Gornist/_larphouse/step/5/блоки/щит_окно.step

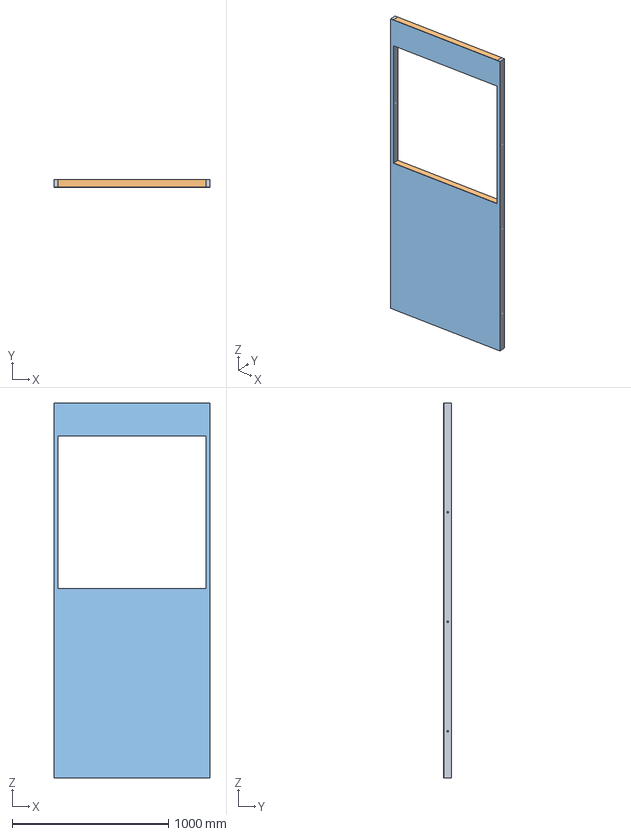
[picture p16: CAD file, 2026-10-09]
step/5/блоки/щит_окно.step
997.0 x 53.0 x 2400.0 mm
стойка_щита_25х50х2400 x 2
перемычка_25х50х947 x 4
обшивка_фанера_3мм_ 997х2400
