Gornist/_larphouse/step/5/блоки/прогон.step

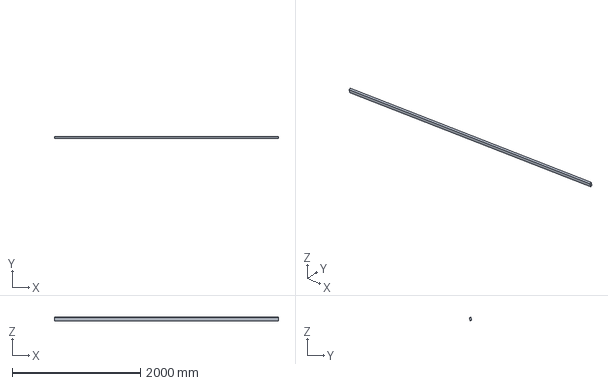
[picture p17: CAD file, 2026-10-09]
step/5/блоки/прогон.step
3500.0 x 38.9 x 55.2 mm
