Gornist/_larphouse/step/6/блоки/полуферма_Б_средняя.step

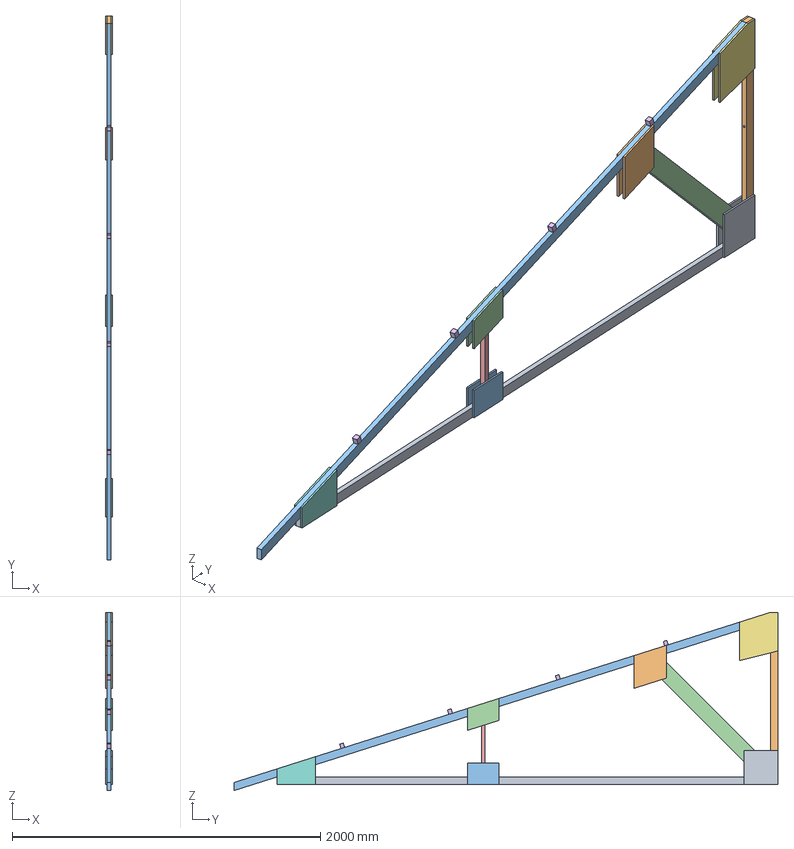
[picture p18: CAD file, 2026-10-09]
step/6/блоки/полуферма_Б_средняя.step
43.0 x 3530.0 x 1156.4 mm
затяжка_25х50х3250
стойка_фермы_25х50х1068
стропило_25х50х3651
подкос_25х50х1066
бабка_25х50х420
лапка_прогона_25х25х30 x 4
косынка_фанера_9 x 12
