Gornist/_larphouse/step/5/блоки/лежень.step

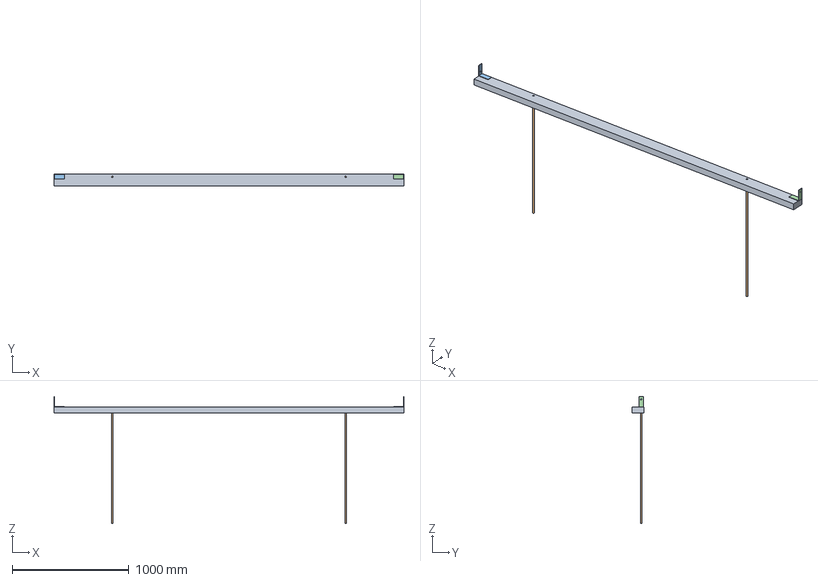
[picture p19: CAD file, 2026-10-09]
step/5/блоки/лежень.step
3000.0 x 100.0 x 1090.0 mm
лежень_50х100х2996
арматура_12х1000 x 2
уголок_90х90х40 x 2
