Gornist/_larphouse/step/5/блоки/щит_дверь.step

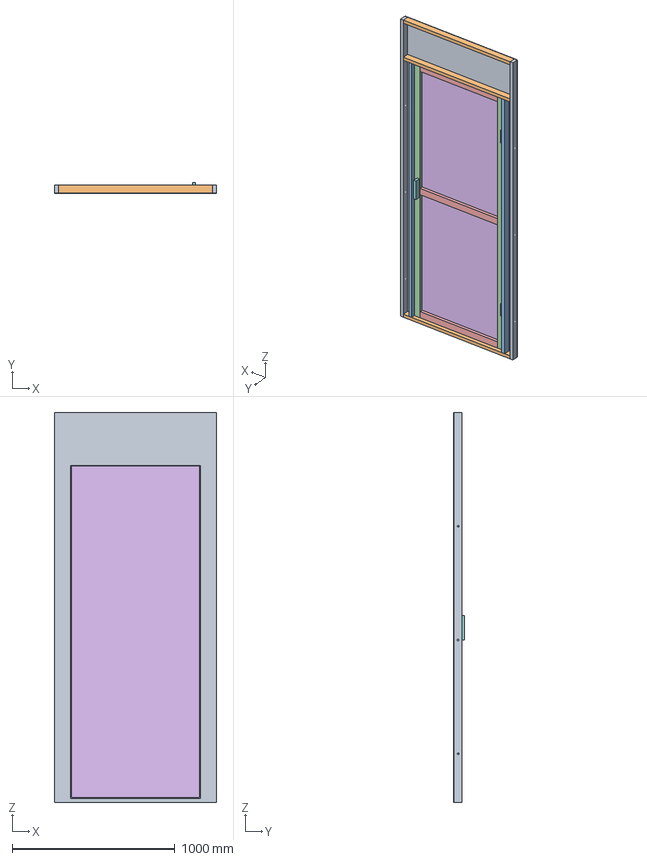
[picture p21: CAD file, 2026-10-09]
step/5/блоки/щит_дверь.step
997.0 x 68.0 x 2400.0 mm
стойка_щита_25х50х2400 x 2
перемычка_25х50х947 x 3
стойка_двери_25х50х2050 x 2
полотно_стойка_25х50х2040 x 2
полотно_перемычка_ 25х50х690.0 x 3
полотно_фанера_790х2040
петля_100 x 2
ручка
обшивка_фанера_3мм_ 997х2400
