Gornist/_larphouse/step/5/блоки/ригель_фронтонный.step

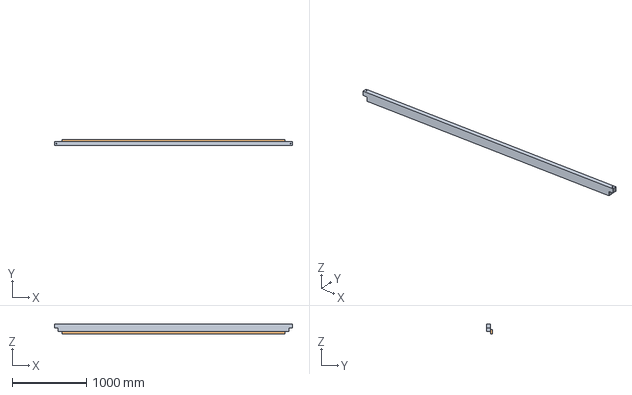
[picture p22: CAD file, 2026-10-09]
step/5/блоки/ригель_фронтонный.step
3200.0 x 79.0 x 130.0 mm
ригель_фронтонный_ 50х100х3200
рейка_упорная_Г_3000
