Gornist/_larphouse/step/5/блоки/ригель_карнизный.step

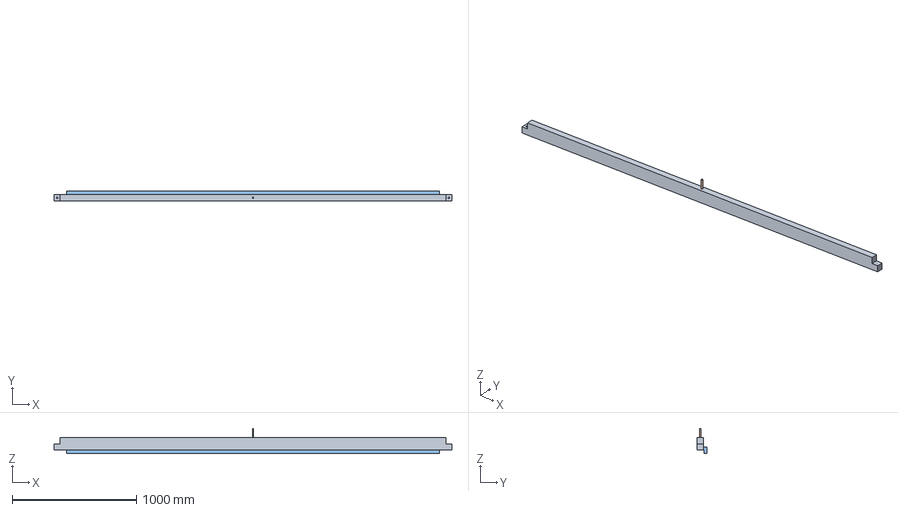
[picture p23: CAD file, 2026-10-09]
step/5/блоки/ригель_карнизный.step
3200.0 x 79.0 x 205.0 mm
ригель_карнизный_ 50х100х3200
штырь_12х165
рейка_упорная_Г_3000
