Gornist/_larphouse/step/5/img/дом_без_тента.png

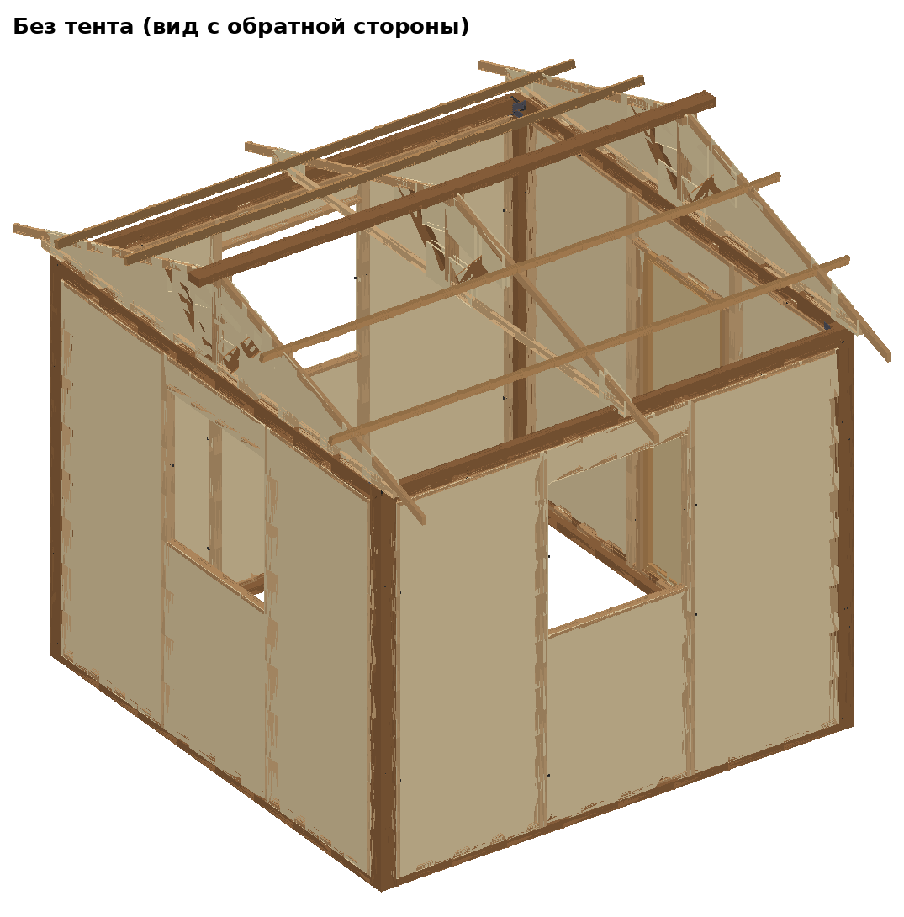
step/5/img/дом_без_тента.png
