Gornist/_larphouse/step/5/img/каркас.png

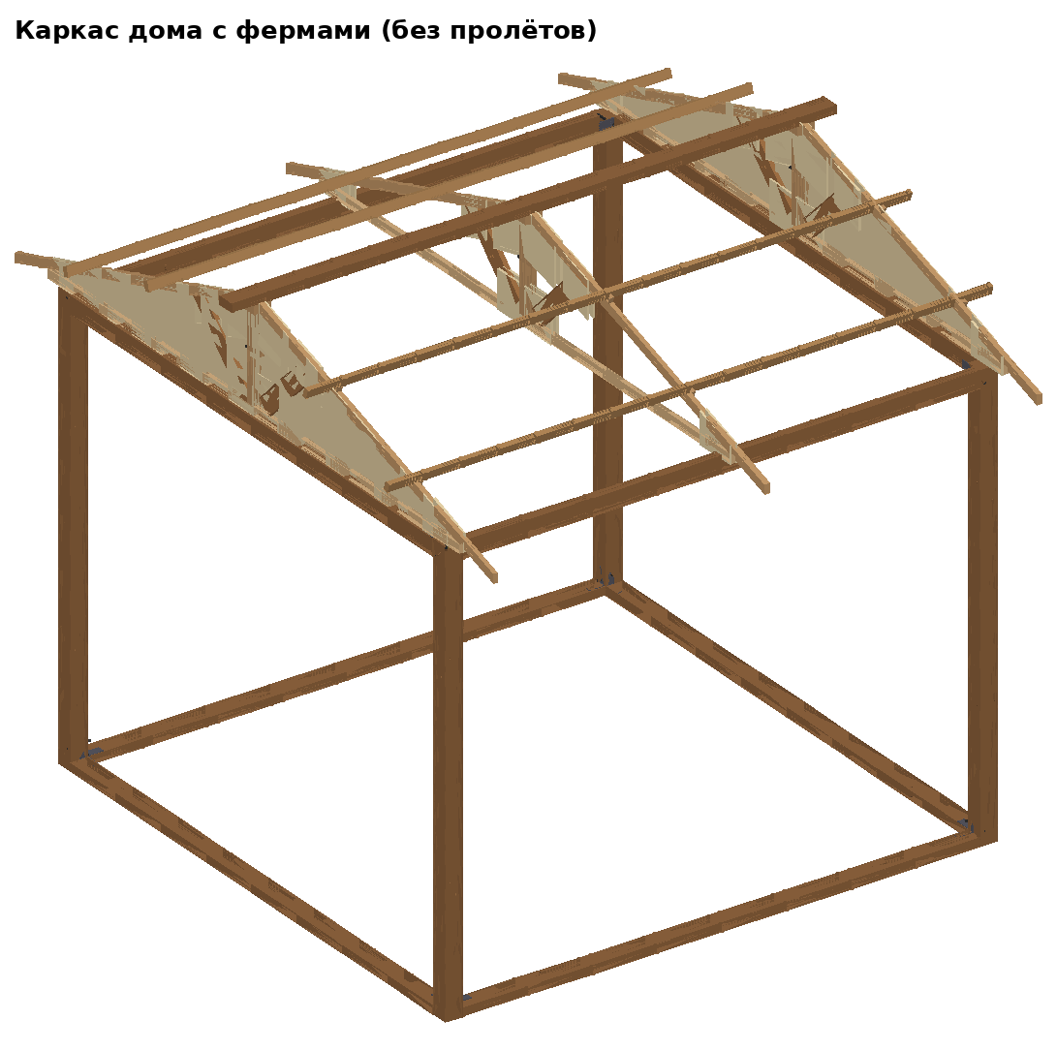
step/5/img/каркас.png
