Gornist/_larphouse/step/5/img/полуферма_фронтон_0.png

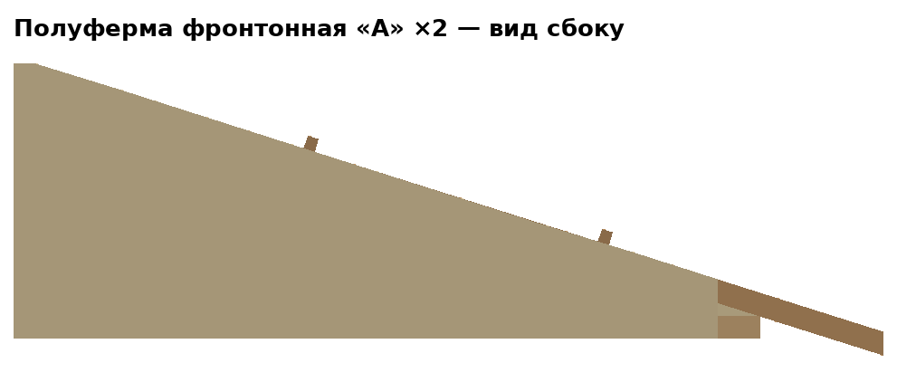
step/5/img/полуферма_фронтон_0.png
