Gornist/_larphouse/step/5/img/полуферма_фронтон_25.png

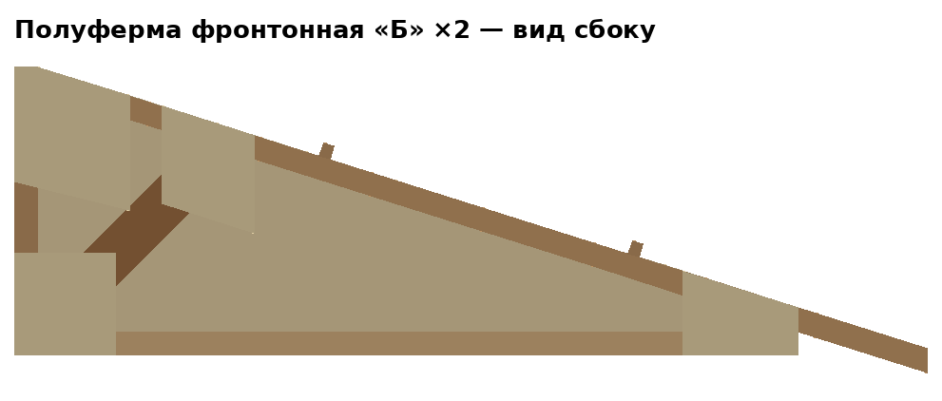
step/5/img/полуферма_фронтон_25.png
