Gornist/_larphouse/step/5/img/пролёт_дверь_снаружи.png

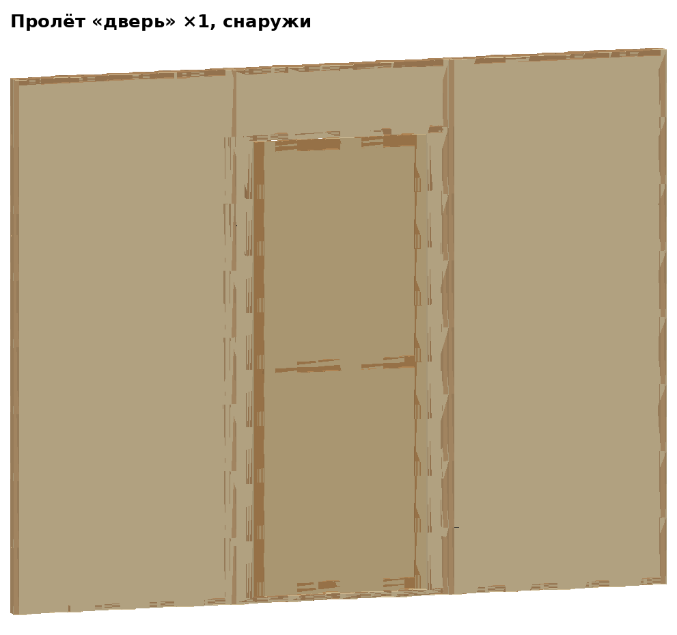
step/5/img/пролёт_дверь_снаружи.png
