Gornist/_larphouse/step/5/img/пролёт_окно_изнутри.png

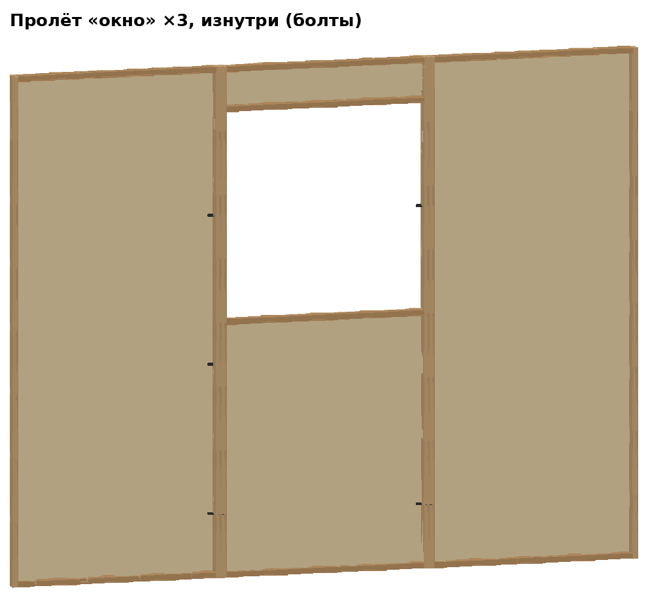
step/5/img/пролёт_окно_изнутри.png
