Gornist/_larphouse/step/6/3х6/img/без_тента.png

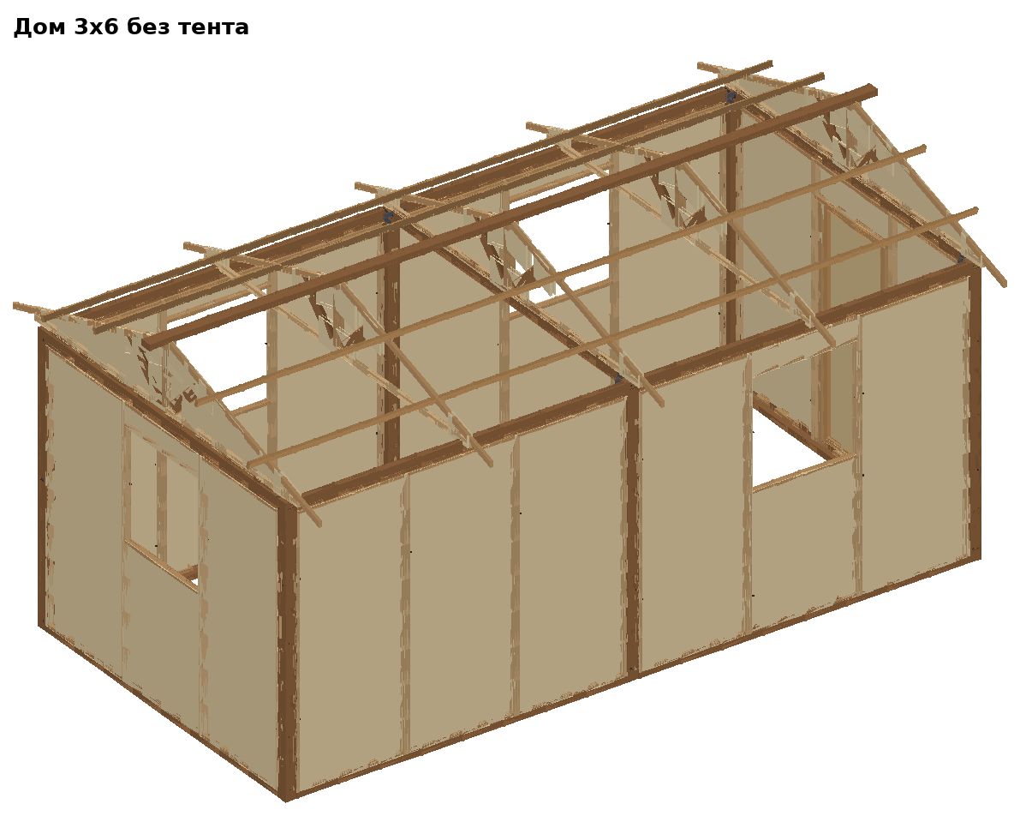
step/6/3х6/img/без_тента.png
