Gornist/_larphouse/step/6/3х6/img/план.png

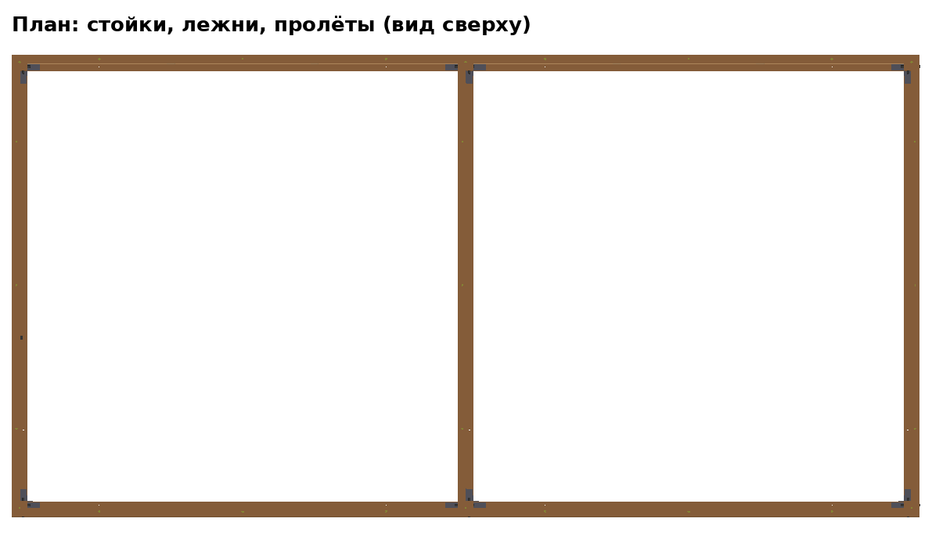
step/6/3х6/img/план.png
