Gornist/_larphouse/step/6/3х9/img/каркас.png

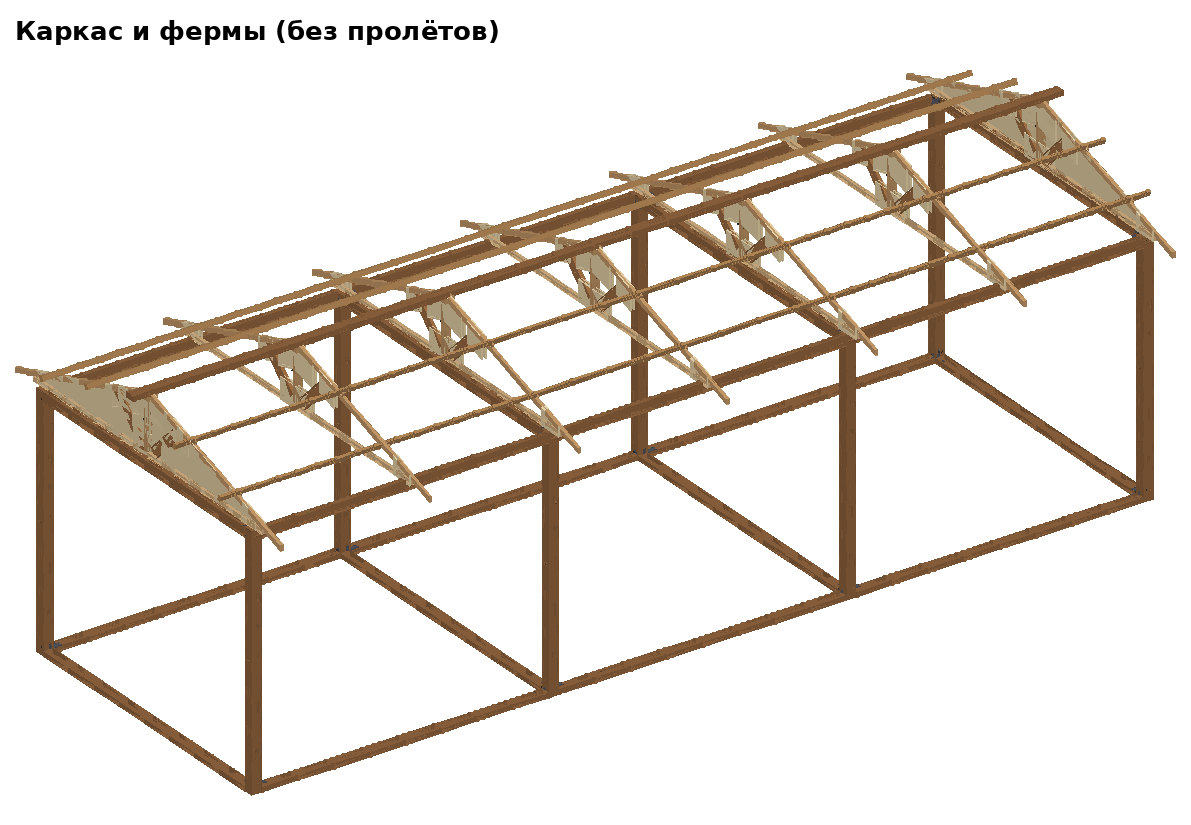
step/6/3х9/img/каркас.png
