Gornist/_larphouse/step/6/3х9/img/план.png

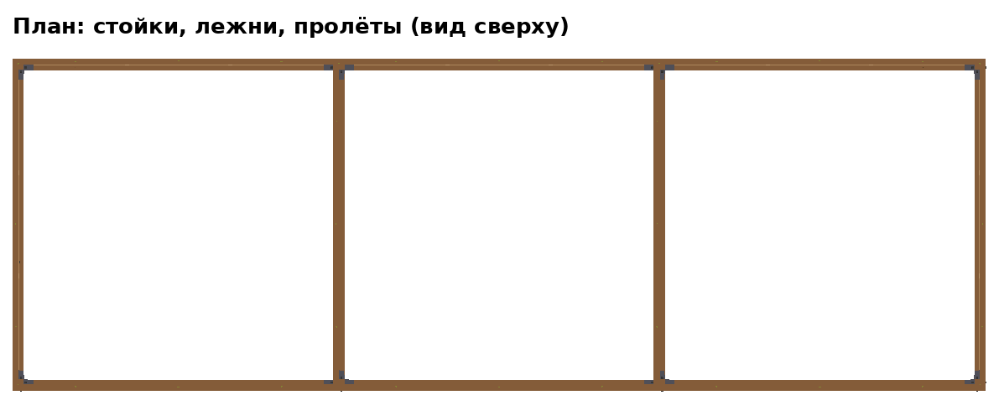
step/6/3х9/img/план.png
