Gornist/_larphouse/step/6/6х6/img/без_тента.png

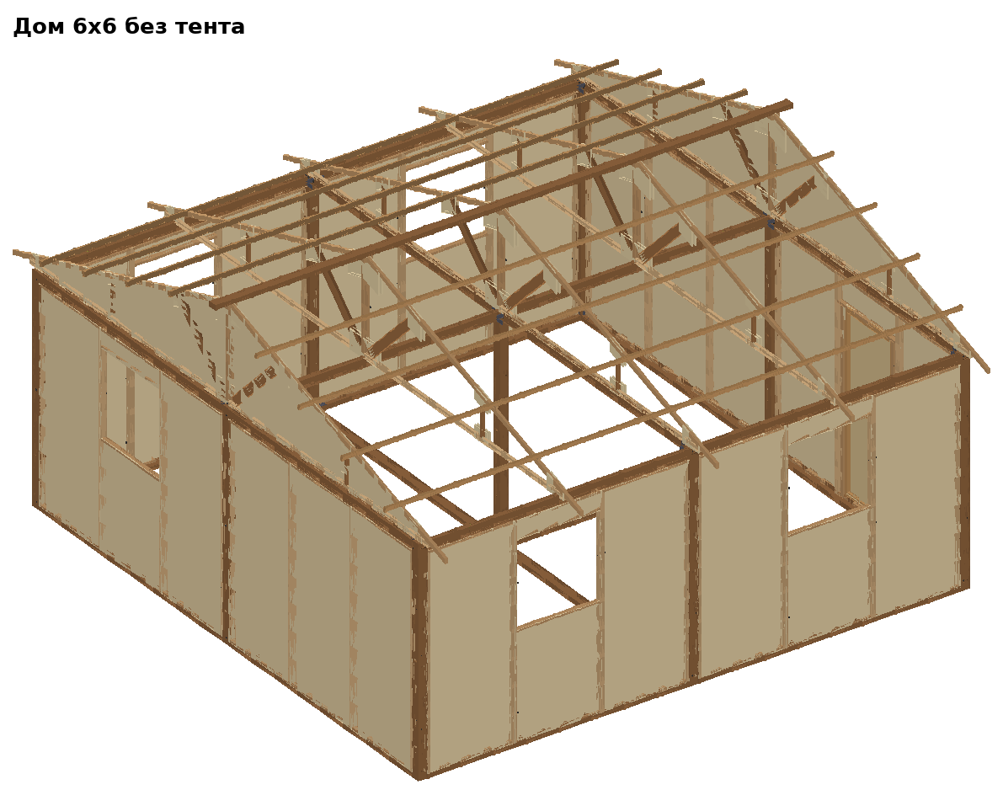
step/6/6х6/img/без_тента.png
