Gornist/_larphouse/step/6/img_детали/полуферма_Б_фронтон_0.png

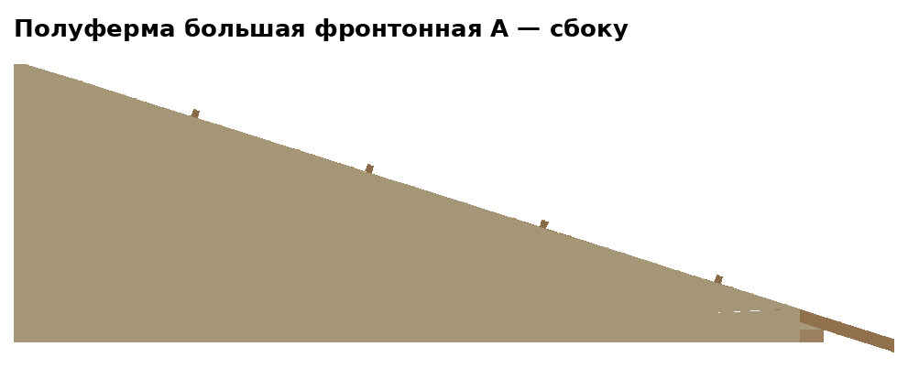
step/6/img_детали/полуферма_Б_фронтон_0.png
