Gornist/_larphouse/step/6/img_детали/полуферма_Б_фронтон_25.png

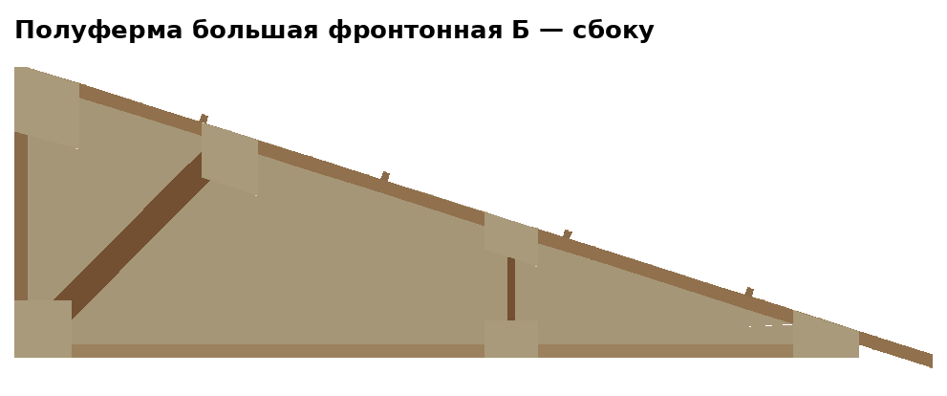
step/6/img_детали/полуферма_Б_фронтон_25.png
