Gornist/_larphouse/step/6/img_детали/стойка.png

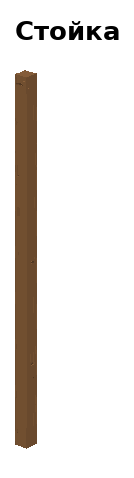
step/6/img_детали/стойка.png
